HSBNE/atmega-18650-discharger/esp32_wifi_bridge/slave_slots.h

#define POSITIONS 30

// Device and Position to Slot number lookup
const slotPosition_t slotPos[POSITIONS] = {
  {3, 13, 1},
  {3, 14, 2},
  {3, 15, 3},
  {3, 7, 4},
  {3, 8, 5},
  {3, 9, 6},
  {2, 12, 7},
  {2, 13, 8},
  {2, 14, 9},
  {2, 15, 10},
  {2, 9, 11},
  {2, 10, 12},
  {2, 11, 13},
  {2, 5, 14},
  {2, 6, 15},
  {2, 7, 16},
  {2, 8, 17},
  {3, 1, 18},
  {3, 2, 19},
  {3, 3, 20},
  {2, 1, 21},
  {2, 2, 22},
  {2, 3, 23},
  {2, 4, 24},
  {3, 10, 25},
  {3, 11, 26},
  {3, 12, 27},
  {3, 4, 28},
  {3, 5, 29},
  {3, 6, 30}
};
